uavopsys/caracas/cots/arm_hub_dimensions.png

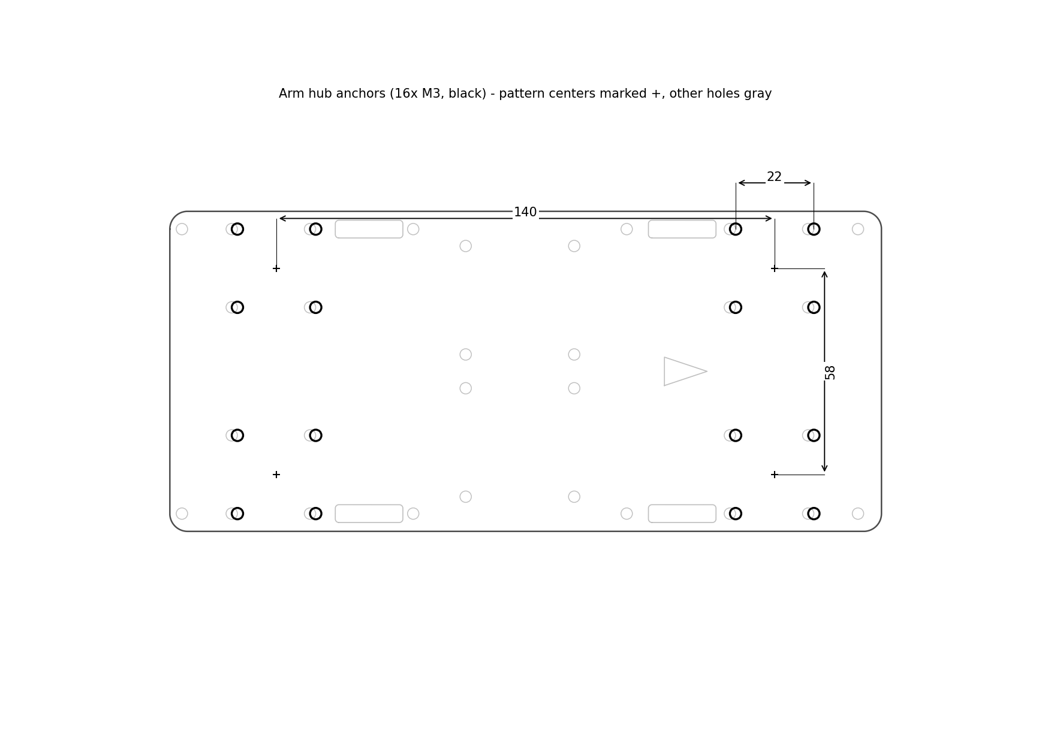
cots/arm_hub_dimensions.png
