uavopsys/caracas/cots/canopy_pads_preview.png

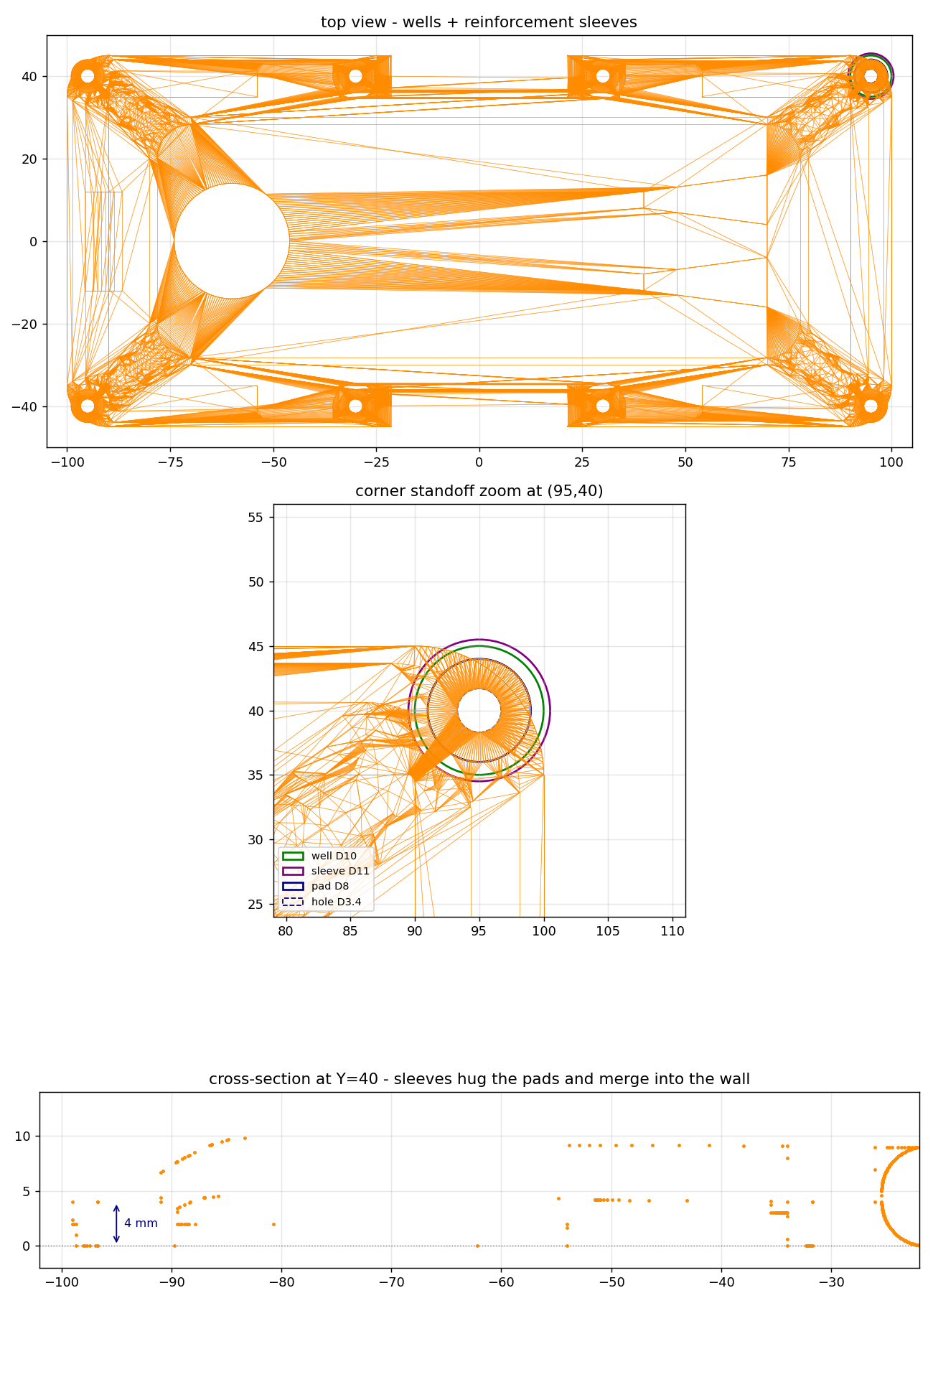
cots/canopy_pads_preview.png
