uavopsys/caracas/cots/canopy_vents_preview.png

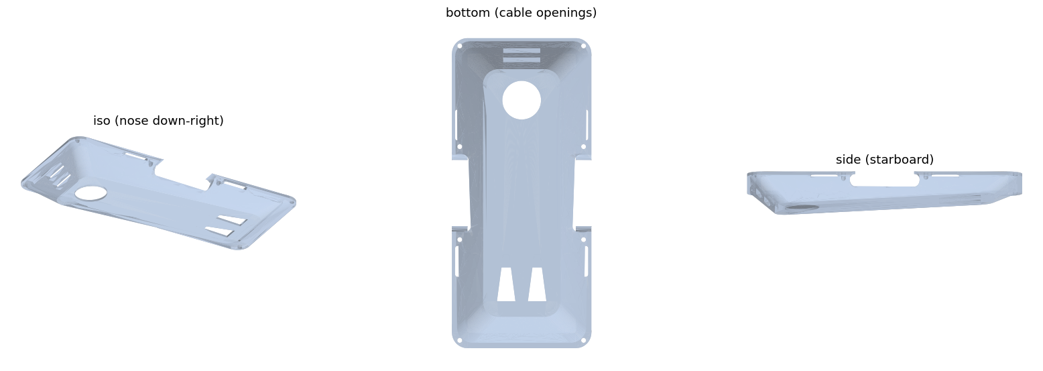
cots/canopy_vents_preview.png
