uavopsys/caracas/cots/gps_holder_preview.png

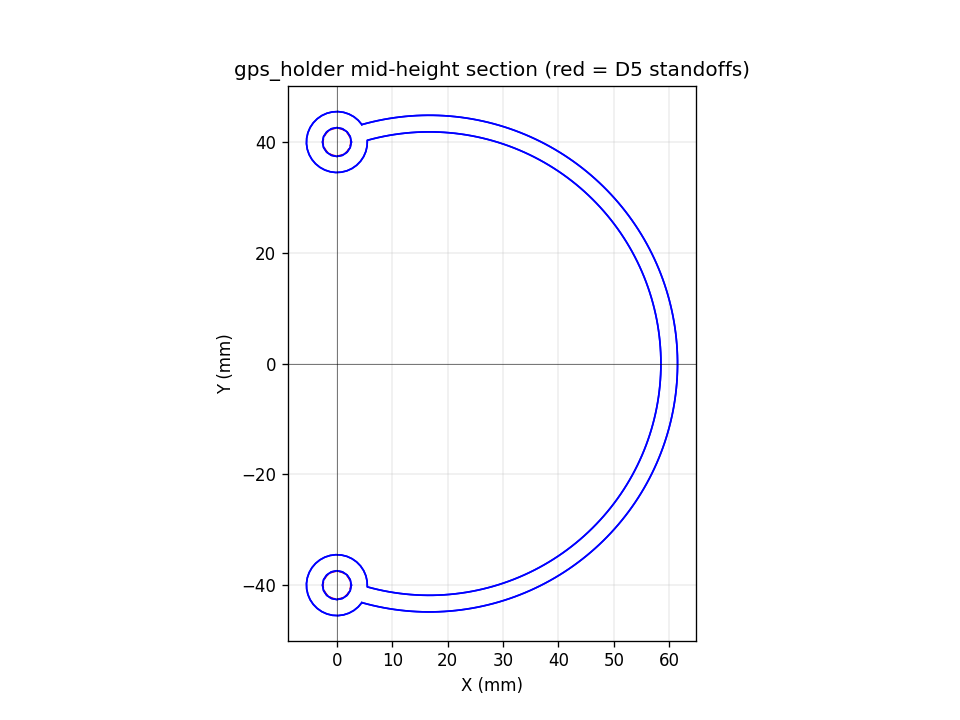
cots/gps_holder_preview.png
