uavopsys/caracas/cots/gps_holder_twist_preview.png

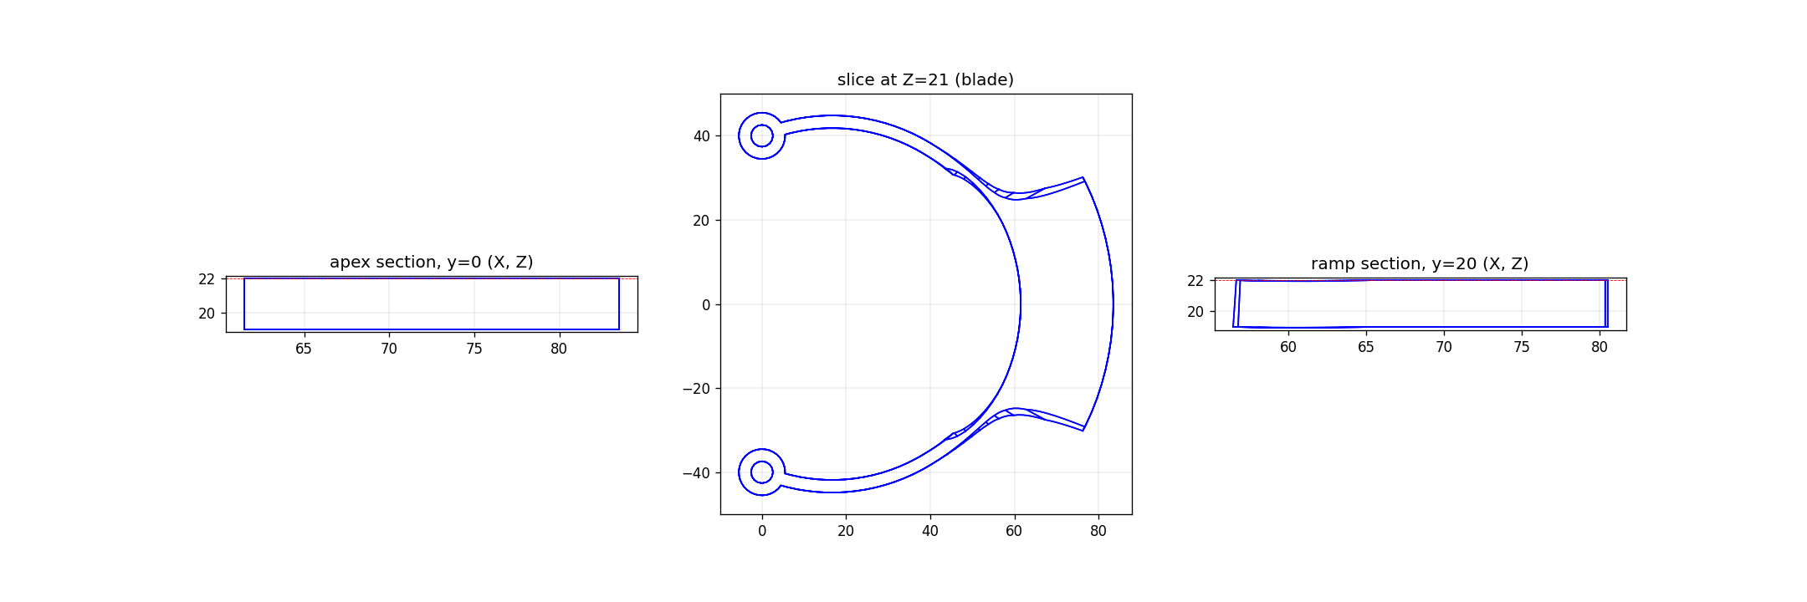
cots/gps_holder_twist_preview.png
