uavopsys/caracas/cots/motor_mount_preview_1.png

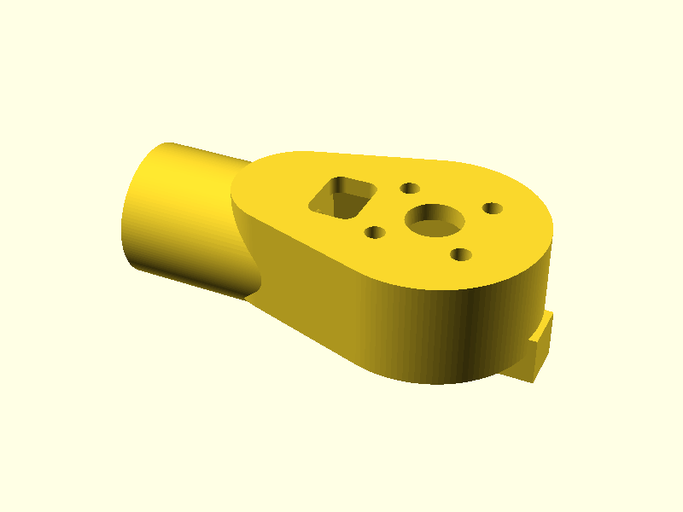
cots/motor_mount_preview_1.png
