uavopsys/caracas/cots/motor_mount_preview_2.png

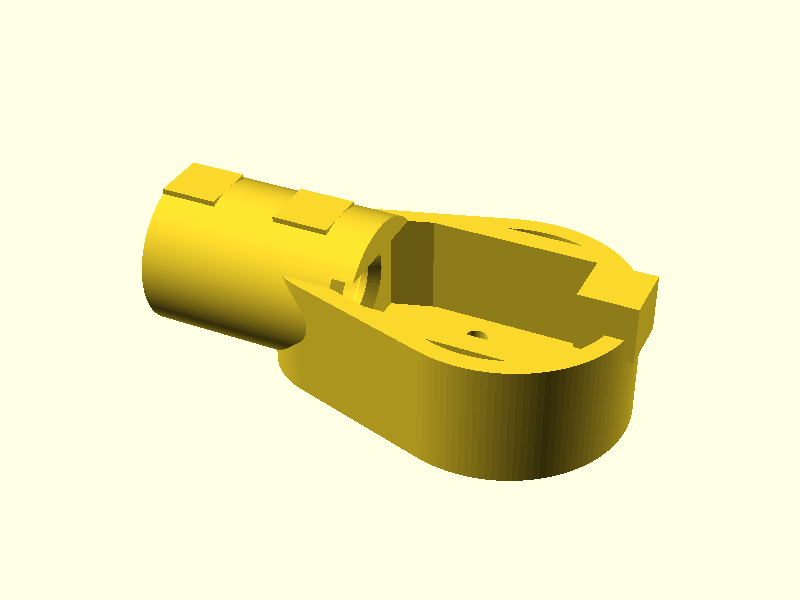
cots/motor_mount_preview_2.png
