uavopsys/caracas/cots/motor_mount_preview_3.png

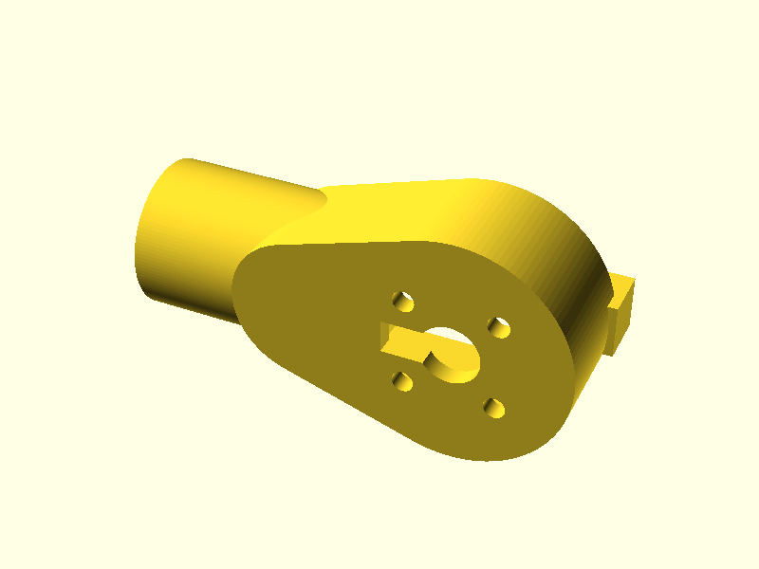
cots/motor_mount_preview_3.png
