uavopsys/caracas/cots/motor_mount_preview_4.png

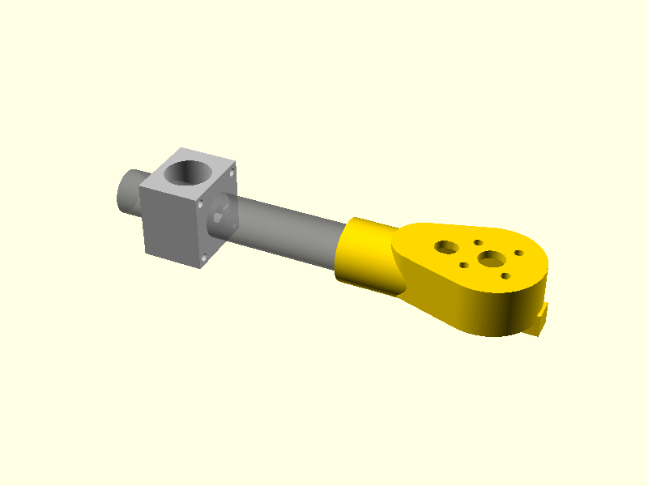
cots/motor_mount_preview_4.png
