uavopsys/caracas/cots/plate_drawing.png

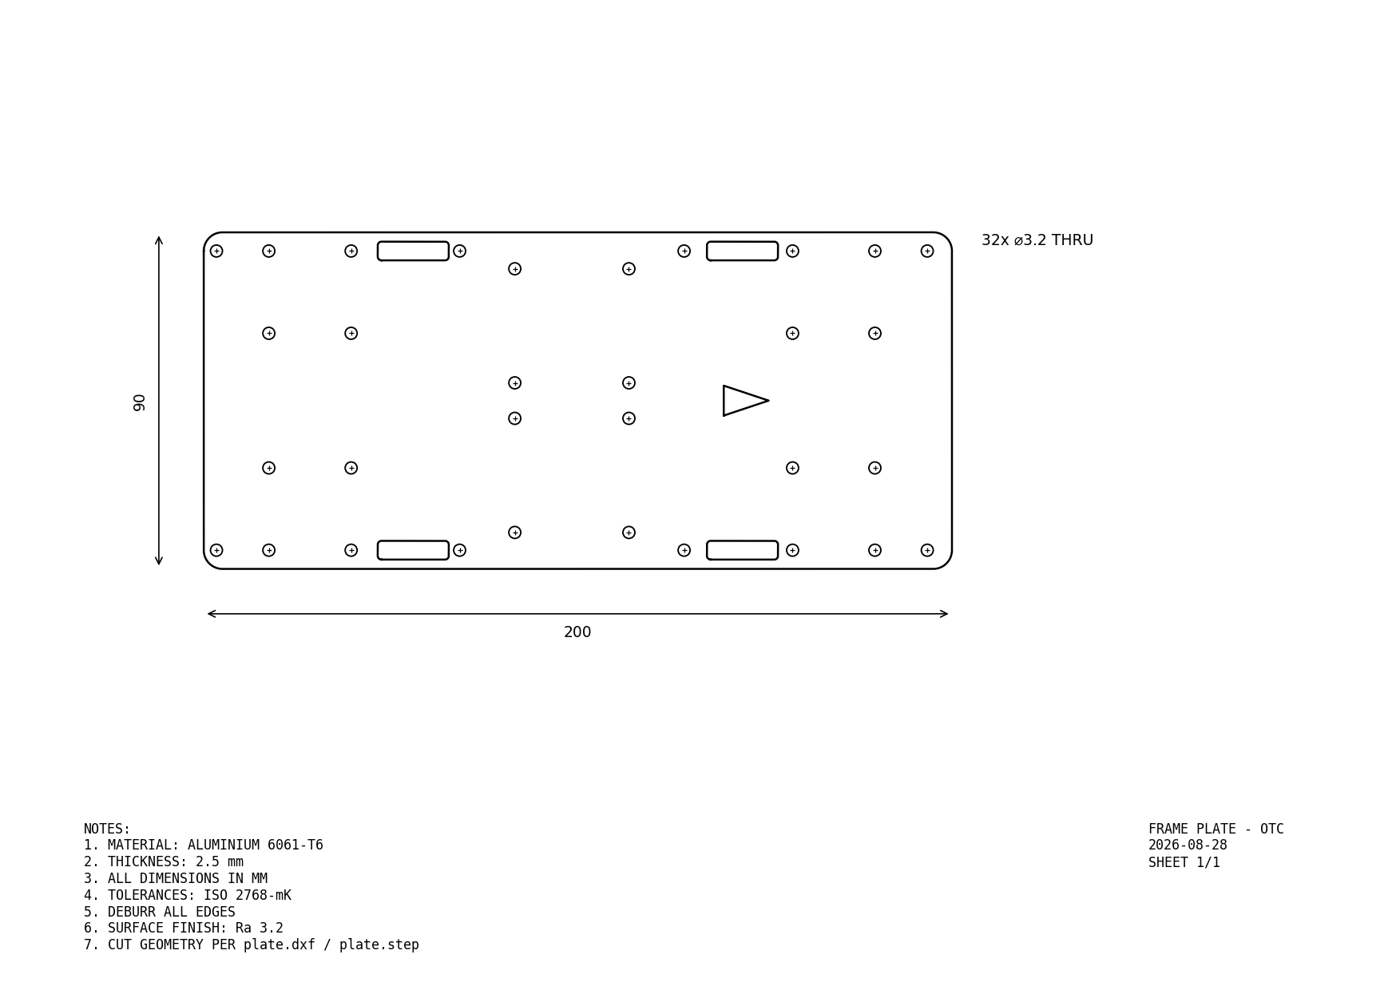
cots/plate_drawing.png
