uavopsys/caracas/cots/standoff_dimensions.png

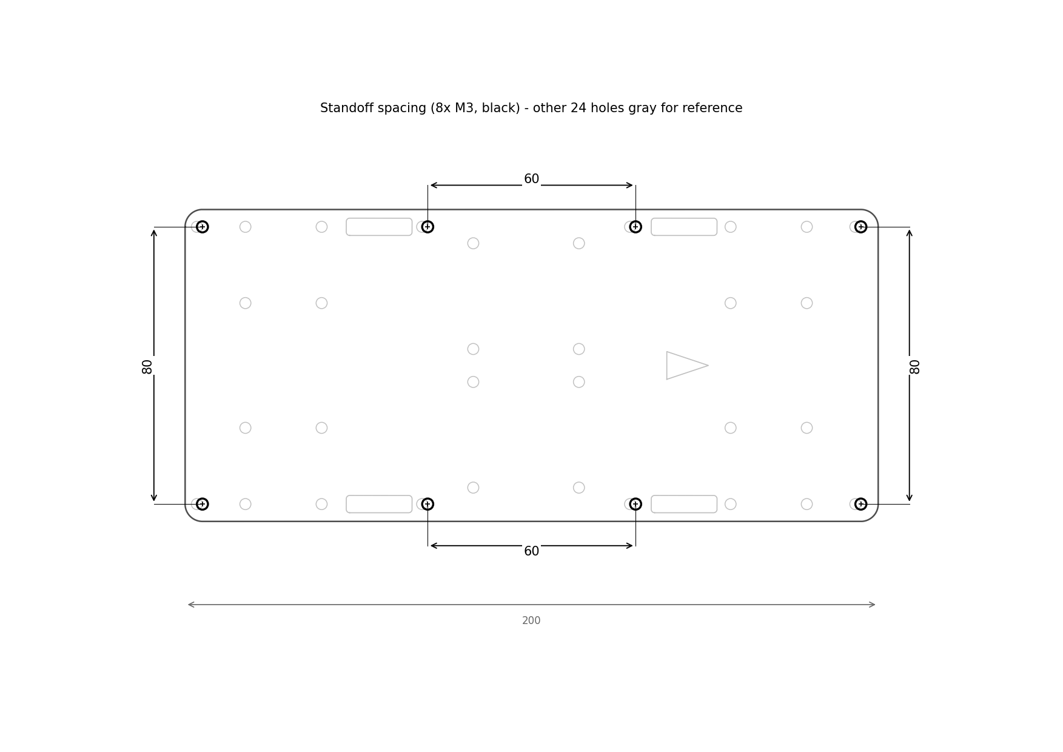
cots/standoff_dimensions.png
