uavopsys/caracas/cots/twist_arm_preview.png

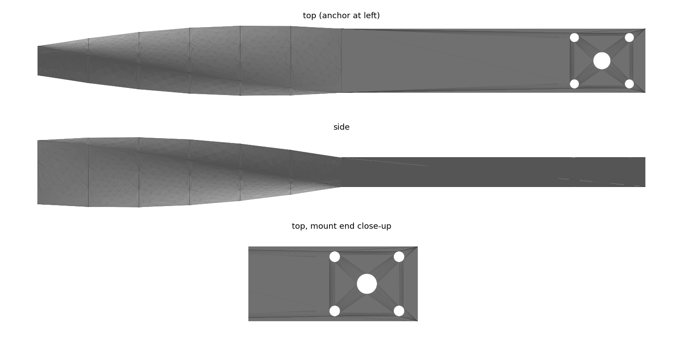
cots/twist_arm_preview.png
